UzixLS/zx-sizif-xxs/fpga/rtl/vencode.vhd

-- Speccy 2010

library ieee;
use ieee.std_logic_1164.all;
use ieee.numeric_std.all;

entity vencode is
    generic(
        freq : integer := 42
    );

    port(
        clk  : in std_logic;
        clk_en  : in std_logic;

        -- Video Input
        videoR : in std_logic_vector(5 downto 0);
        videoG : in std_logic_vector(5 downto 0);
        videoB : in std_logic_vector(5 downto 0);

        videoHS_n : in std_logic;
        videoVS_n : in std_logic;
        videoPS_n : in std_logic;

        -- Video Output
        videoY    : out std_logic_vector(7 downto 0);
        videoC    : out std_logic_vector(7 downto 0);
        videoV    : out std_logic_vector(7 downto 0)
    );
end vencode;

architecture rtl of vencode is
    signal carrier  : unsigned(7 downto 0);

    signal vcounter : unsigned(8 downto 0);
    signal hcounter : unsigned(12 downto 0);

    signal burphase : unsigned(1 downto 0) := "00";

    signal window_v : std_logic;
    signal window_h : std_logic;
    signal window_c : std_logic;

    signal ivideoR  : unsigned(5 downto 0);
    signal ivideoG  : unsigned(5 downto 0);
    signal ivideoB  : unsigned(5 downto 0);

    signal Y1 : unsigned(13 downto 0);
    signal Y2 : unsigned(13 downto 0);
    signal Y3 : unsigned(13 downto 0);
    signal U1 : unsigned(13 downto 0);
    signal U2 : unsigned(13 downto 0);
    signal U3 : unsigned(13 downto 0);
    signal V1 : unsigned(13 downto 0);
    signal V2 : unsigned(13 downto 0);
    signal V3 : unsigned(13 downto 0);

    signal burstUV  : signed(13 downto 0);

    signal prevY : signed(13 downto 0);
    signal prevU : signed(13 downto 0);
    signal prevV : signed(13 downto 0);
    signal prevC : signed(23 downto 0);

    signal inSin : std_logic_vector(15 downto 0);
    signal inCos : std_logic_vector(15 downto 0);
    signal sin  : signed(15 downto 0);
    signal cos  : signed(15 downto 0);
    signal pcos : signed(15 downto 0);

    signal Um : signed(23 downto 0);
    signal Vm : signed(23 downto 0);

    signal Y : signed(7 downto 0);
    signal U : signed(7 downto 0);
    signal V : signed(7 downto 0);
    signal C : signed(7 downto 0);

    constant vref : signed(13 downto 0) := to_signed( 54, 8 ) & "000000";
    constant cent : signed(7 downto 0) := X"80";

    component vencode_sin_cos
        port(
            clk : in std_logic;
            phase : in std_logic_vector(7 downto 0);
            sinus : out std_logic_vector(15 downto 0);
            cosinus : out std_logic_vector(15 downto 0)
        );
    end component;  
begin

    process(clk, clk_en )
        variable carrierCounter :   unsigned(15 downto 0);
    begin
        if ( clk'event and clk = '1' and clk_en = '1' ) then
            carrierCounter := carrierCounter + 157;
            if carrierCounter >= 6552 then
                carrier <= carrier + 28;        
                carrierCounter := carrierCounter - 6552;
            else            
                carrier <= carrier + 27;
            end if;         
        end if;
    end process;

    vencode_sin_cos0 : vencode_sin_cos port map( clk, std_logic_vector( carrier ), inSin, inCos );
    sin <= signed( inSin( 15 downto 0 ) );
    cos <= signed( inCos( 15 downto 0 ) );
    pcos <= cos when burphase(0) = '0' else -cos;

    process(clk, clk_en )
        variable ivideoVS_n : std_logic;
        variable ivideoHS_n : std_logic;
    begin
        if ( clk'event and clk = '1' and clk_en = '1' ) then
            Y <= prevY( 13 downto 6 );
            Um <= U * sin;
            Vm <= V * pcos;

            videoY <= std_logic_vector( Y );
            videoC <= std_logic_vector( cent + C );
            videoV <= std_logic_vector( Y + C );

            ivideoR <= unsigned( videoR );
            ivideoG <= unsigned( videoG );
            ivideoB <= unsigned( videoB );
            if ( videoHS_n = '0' and ivideoHS_n = '1' ) then
                vcounter <= vcounter + 1;
                burphase <= burphase - 1;
                hcounter <= ( others => '0' );          
            else            
                hcounter <= hcounter + 1;
            end if;

            if (videoVS_n = '0' and ivideoVS_n = '1') then
                vcounter <= ( others => '0' );
            end if;

            if ( vcounter = ( 10 - 1 ) ) then
                window_v <= '1';
            elsif ( vcounter = ( 310 - 1 ) ) then
                window_v <= '0';
            end if;

            if (hcounter = ( integer( 10.5 * real( freq ) ) - 1 ) ) then
                window_h <= '1';
            elsif ( hcounter = ( integer( 62.5 * real( freq ) ) - 1 ) ) then
                window_h <= '0';
            end if;

            if ( hcounter = ( integer( 5.6 * real( freq ) ) - 1 ) ) then
                window_c <= '1';
            elsif ( hcounter = ( integer( 8.1 * real( freq ) ) - 1 ) ) then
                window_c <= '0';
            end if;

            ivideoVS_n := videoVS_n;
            ivideoHS_n := videoHS_n;
        end if;
    end process;

--  Y =  0.299 R + 0.587 G + 0.114 B
--  U = -0.147 R - 0.289 G + 0.436 B
--  V =  0.615 R - 0.515 G - 0.100 B

    Y1 <= ( to_unsigned( 38, 8 ) * ivideoR );
    Y2 <= ( to_unsigned( 75, 8 ) * ivideoG );
    Y3 <= ( to_unsigned( 15, 8 ) * ivideoB );

    U1 <= ( to_unsigned( 19, 8 ) * ivideoR );
    U2 <= ( to_unsigned( 37, 8 ) * ivideoG );
    U3 <= ( to_unsigned( 56, 8 ) * ivideoB );

    V1 <= ( to_unsigned( 79, 8 ) * ivideoR );
    V2 <= ( to_unsigned( 66, 8 ) * ivideoG );
    V3 <= ( to_unsigned( 13, 8 ) * ivideoB );   

    prevY <= to_signed( 0, 14 ) when videoPS_n = '0' else
        vref + signed( Y1 + Y2 + Y3 ) when ( window_h = '1' and window_v = '1' ) else
        vref;

    burstUV <= to_signed( 20, 8 ) & "000000" when ( window_c = '1' and window_v = '1' ) else
        ( others => '0' );
    prevU <= signed( U3 - U1 - U2 ) when ( window_h = '1' and window_v = '1' ) else 
        ( -burstUV );
    prevV <= signed( V1 - V2 - V3 ) when ( window_h = '1' and window_v = '1' ) else
        ( burstUV );

    U <= prevU( 13 downto 6 );
    V <= prevV( 13 downto 6 );
    prevC <= Um + Vm;
    C <= prevC( 23 downto 16 );

end rtl;
